IAlmostDeveloper/remote-control-esp/WemosRemote/WemosRemote.h

#include <SPI.h>
#include <Wire.h>
#include <ESP8266WiFi.h>
#include <ESP8266WebServer.h>
#include <PubSubClient.h>
#include <ArduinoJson.h>
#include <Arduino.h>
#include <IRremoteESP8266.h>
#include <IRsend.h>
#include <IRrecv.h>
#include <IRutils.h>
#include "UserData.h"
#include "Files.h"
#include "Connections.h"
#include "Controls.h"
#include "Web.h"
#include "Reset.h"

unsigned long getCodeFromPayload(byte* payload, unsigned int length);
unsigned long receiveCode();
void sendCode(byte* payload, unsigned int length, String encoding);
void subscribeToAllTopics();
bool connectToWiFi();
bool connectToMQTT();
void handleRoot();
char* convertToCharArray(String str);
void loadPage(String page);
void wifiSetup();
void mqttSetup();
void wifiSubmit();
void mqttSubmit();
String getStringFromFile(String path);
void writeStringToFile(String str, String path);
