IAlmostDeveloper/remote-control-esp/WemosRemote/UserData.h

char *ssid = "";
char *pass = "";
char *mqtt_server = "";
int mqtt_port = 0;
char *mqtt_user = "";
char *mqtt_pass = "";
char* mqtt_topics[] = {"remoteControl/devices/1/code/RC5Controller", 
                            "remoteControl/devices/1/code/NECController", 
                            "remoteControl/devices/1/receive"};
